RoboTakao/NX25/NX25_M5AtomS3_JoyC_ik/Data/NX25.bmp

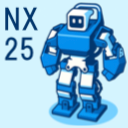
NX25_M5AtomS3_JoyC_ik/Data/NX25.bmp
