RoboTakao/NX25/NX25_STL/UpperCover_Plate_B.stl

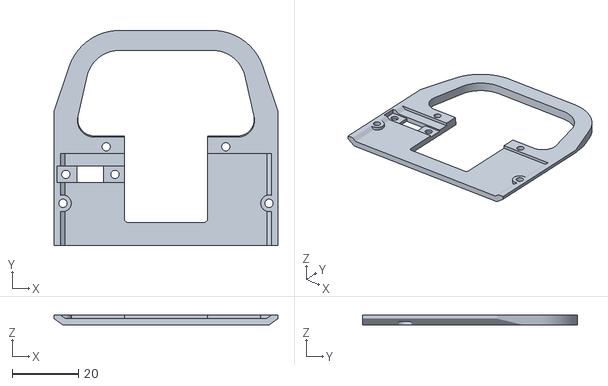
[picture p21: CAD file, 2025-08-03]
NX25_STL/UpperCover_Plate_B.stl
67.4 x 64.7 x 3.00
