RoboTakao/NX25/NX25_STL/Pipe_B.stl

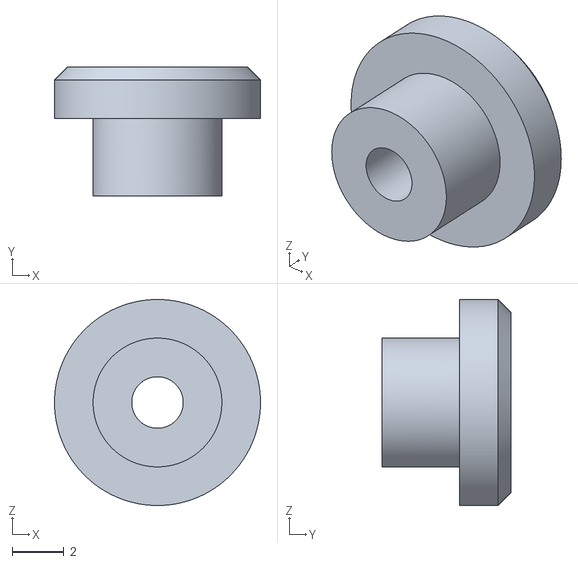
[picture p22: CAD file, 2025-08-03]
NX25_STL/Pipe_B.stl
8.00 x 5.00 x 8.00
