RoboTakao/NX25/NX25_STL/Bracket02_W.stl

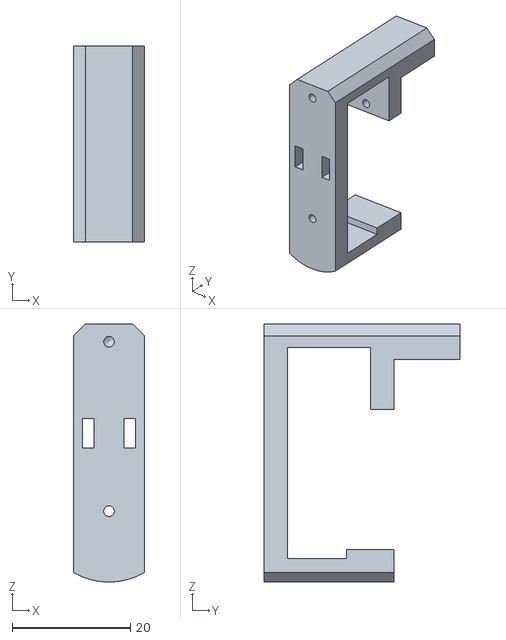
[picture p23: CAD file, 2025-08-03]
NX25_STL/Bracket02_W.stl
12.0 x 33.2 x 43.7
