RoboTakao/NX25/NX25_STL/UpperCover_F_B.stl

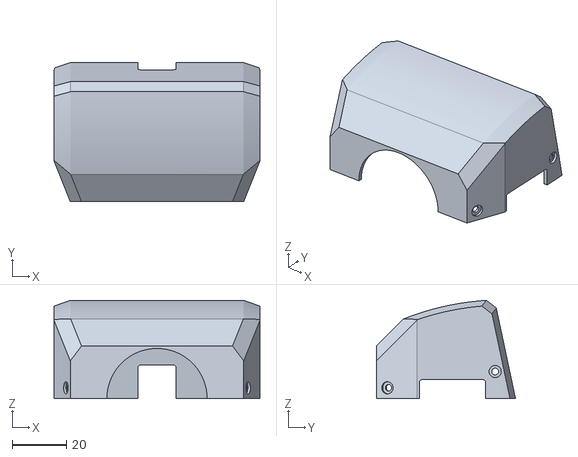
[picture p24: CAD file, 2025-08-03]
NX25_STL/UpperCover_F_B.stl
76.0 x 51.3 x 36.3
