RoboTakao/NX25/NX25_STL/Nee_B.stl

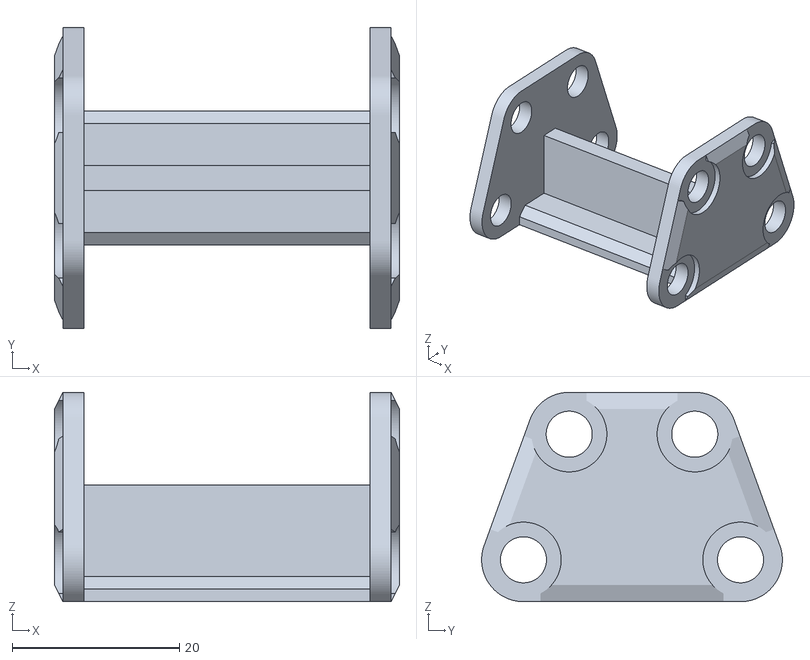
[picture p25: CAD file, 2025-08-03]
NX25_STL/Nee_B.stl
41.2 x 35.9 x 25.0
