RoboTakao/NX25/NX25_STL/Spacer02_B.stl

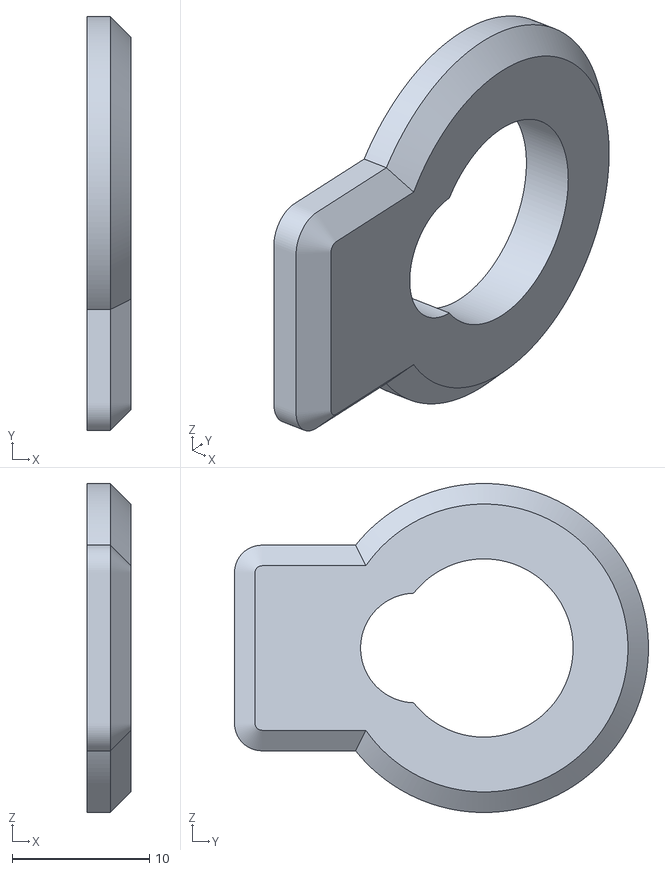
[picture p26: CAD file, 2025-08-03]
NX25_STL/Spacer02_B.stl
3.20 x 30.2 x 24.0
